Sreejakb/IoT-based-Data-Monitor-and-Alert-System/Circuit Diagram/C2.jpg

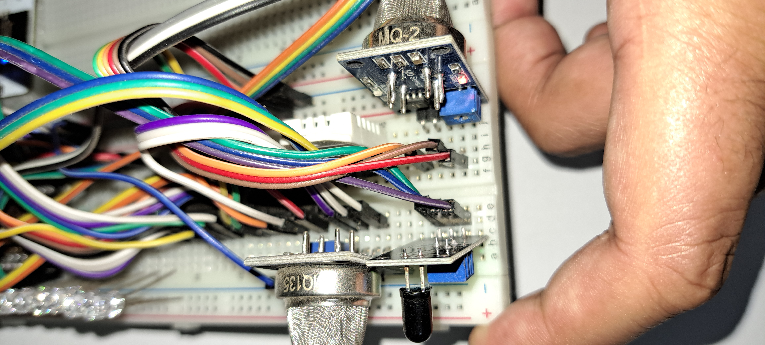
Circuit Diagram/C2.jpg
