Sreejakb/IoT-based-Data-Monitor-and-Alert-System/Circuit Diagram/C3.jpg

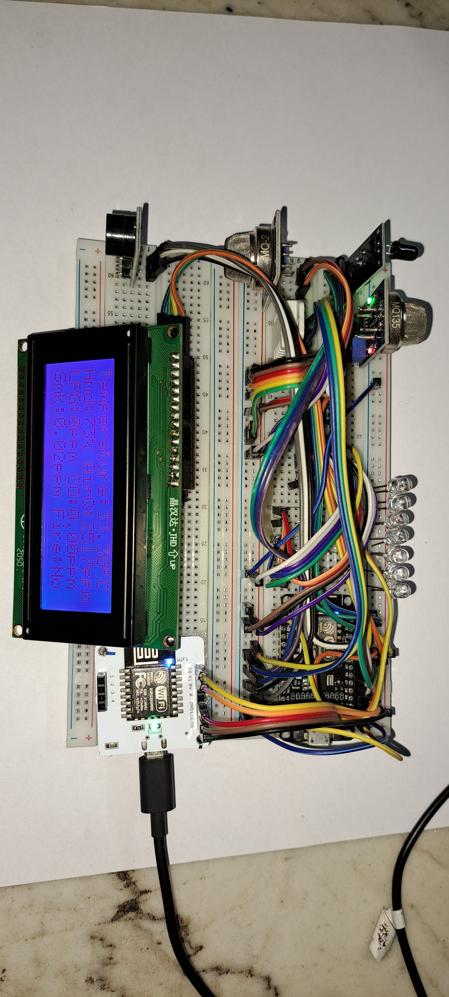
Circuit Diagram/C3.jpg
