Sreejakb/IoT-based-Data-Monitor-and-Alert-System/Circuit Diagram/C5.jpg

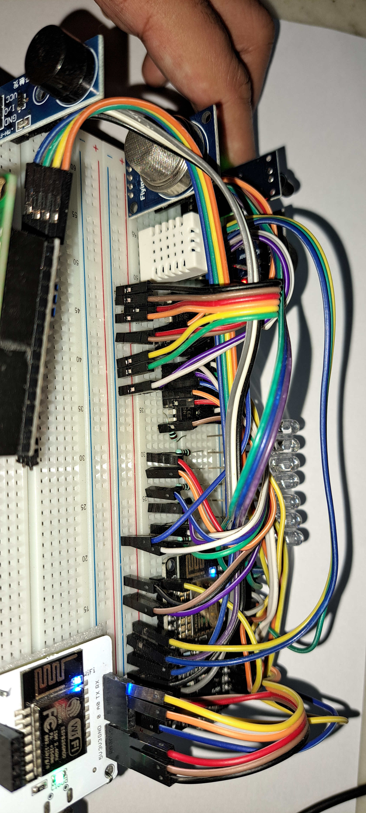
Circuit Diagram/C5.jpg
