Sreejakb/IoT-based-Data-Monitor-and-Alert-System/Circuit Diagram/C6.jpg

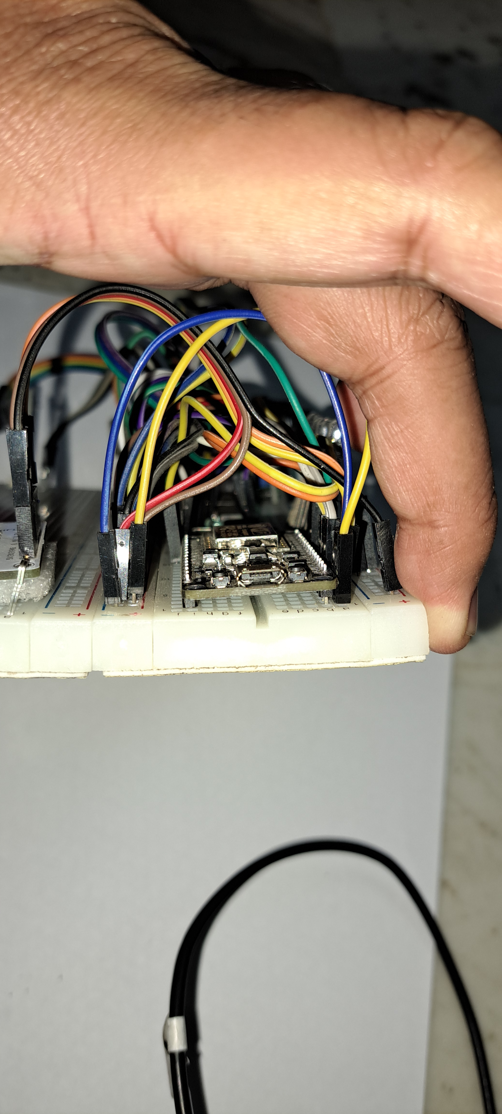
Circuit Diagram/C6.jpg
