Sreejakb/IoT-based-Data-Monitor-and-Alert-System/Screenshot/S3.jpg

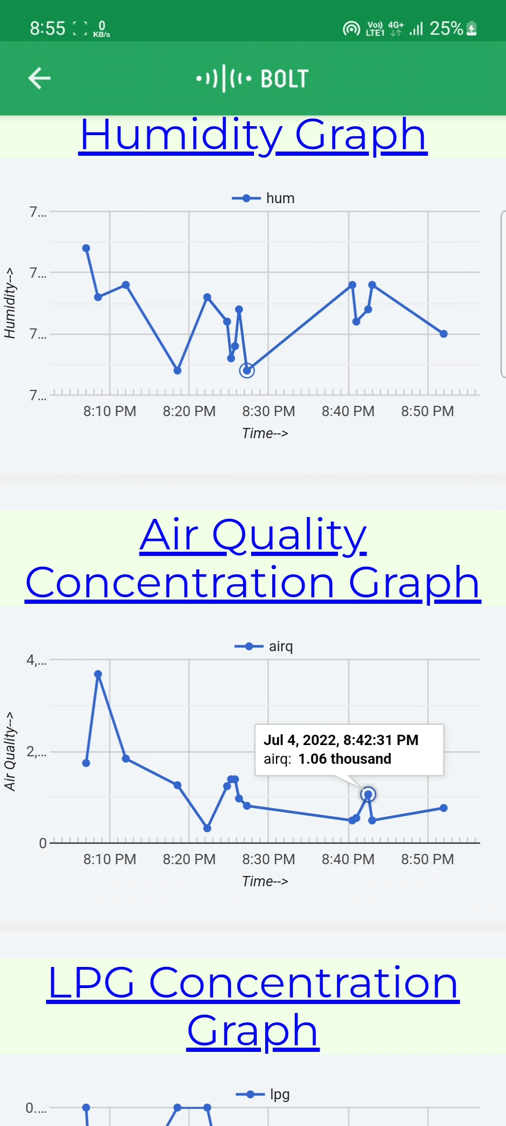
Screenshot/S3.jpg
