Sreejakb/IoT-based-Data-Monitor-and-Alert-System/Screenshot/S4.jpg

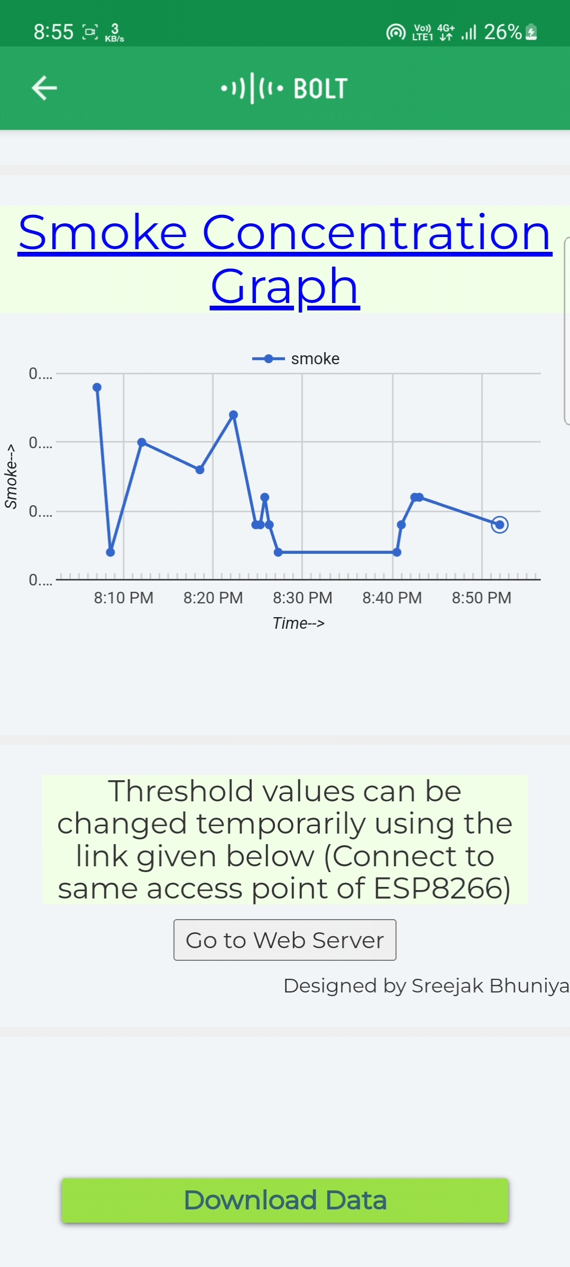
Screenshot/S4.jpg
