Sreejakb/IoT-based-Data-Monitor-and-Alert-System/Screenshot/S6.jpg

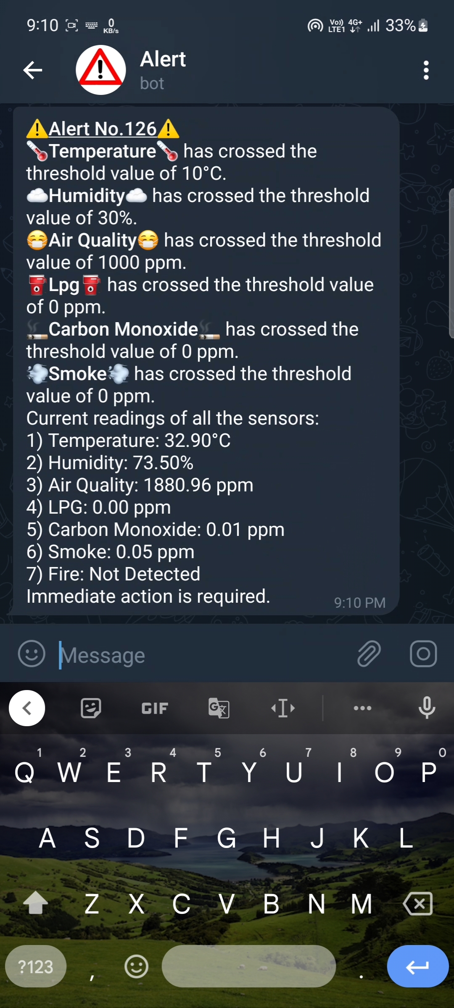
Screenshot/S6.jpg
